pete-restall/MsfOwlClock/src/models/ferrite-rod-antenna/ferrite-rod-antenna.step

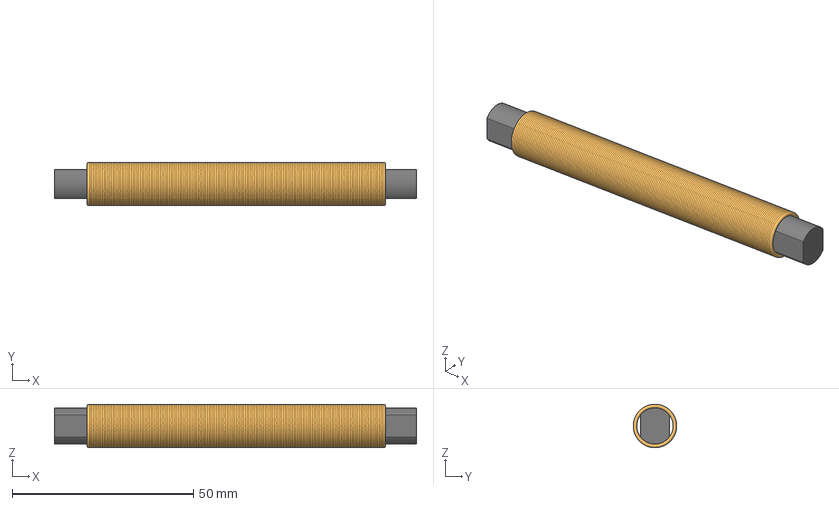
[picture p6: CAD file, 2024-04-20]
src/models/ferrite-rod-antenna/ferrite-rod-antenna.step
100.0 x 12.0 x 12.0 mm
Rod
Loop1 x 5
Loop2 x 5
Loop3 x 5
Loop4 x 5
Loop005 x 5
Loop006 x 5
Loop007 x 5
Loop008 x 5
Loop009 x 5
Loop010 x 5
Loop011 x 5
Loop012 x 5
Loop013 x 5
Loop014 x 5
Loop015 x 5
Loop016 x 5
Loop017 x 5
Loop018 x 5
Loop019 x 5
Loop020 x 5
Loop021 x 5
Loop022 x 5
Loop023 x 5
Loop024 x 5
Loop025 x 5
Loop026 x 5
Loop027 x 5
Loop028 x 5
Loop029 x 5
Loop030 x 5
Loop031 x 5
Loop032 x 5
Loop033 x 5
Loop034 x 5
Loop035 x 5
Loop036 x 5
Loop037 x 5
Loop038 x 5
Loop039 x 5
Loop040 x 5
Loop041 x 5
Loop042 x 5
Loop043 x 5
Loop044 x 5
Loop045 x 5
Loop046 x 5
Loop047 x 5
Loop048 x 5
Loop049 x 5
Loop050 x 5
Loop051 x 5
Loop052 x 5
Loop053 x 5
Loop054 x 5
Loop055 x 5
Loop056 x 5
Loop057 x 5
Loop058 x 5
Loop059 x 5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
